nils-eilers/uMMF/doc/8032030-6.gif

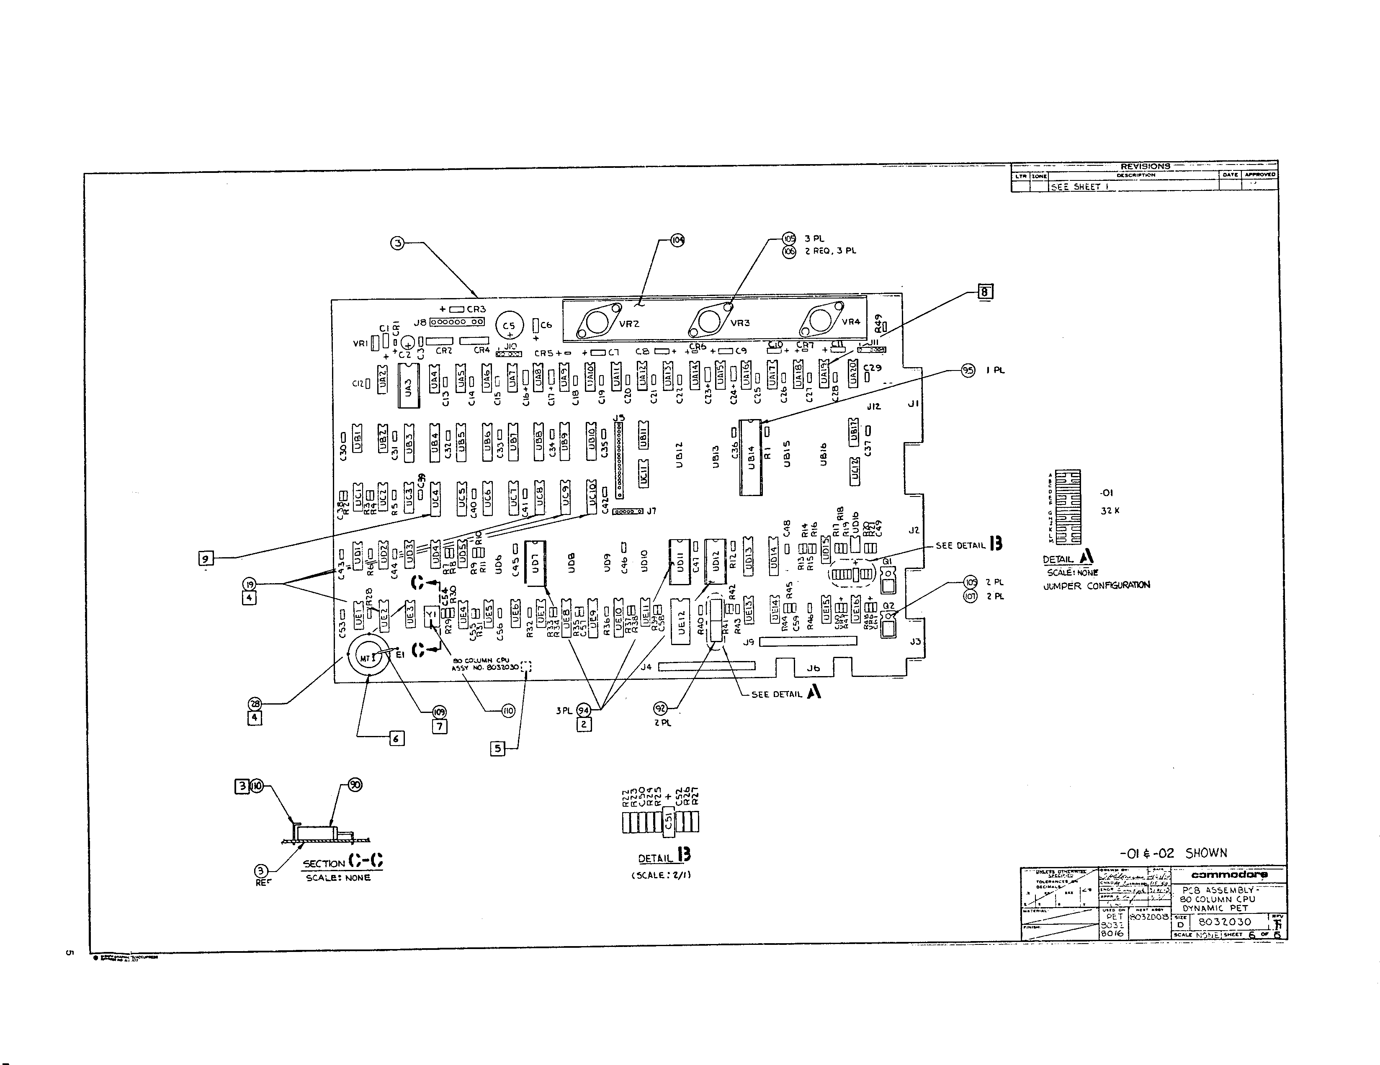
doc/8032030-6.gif
