nils-eilers/uMMF/doc/8032080-7.gif

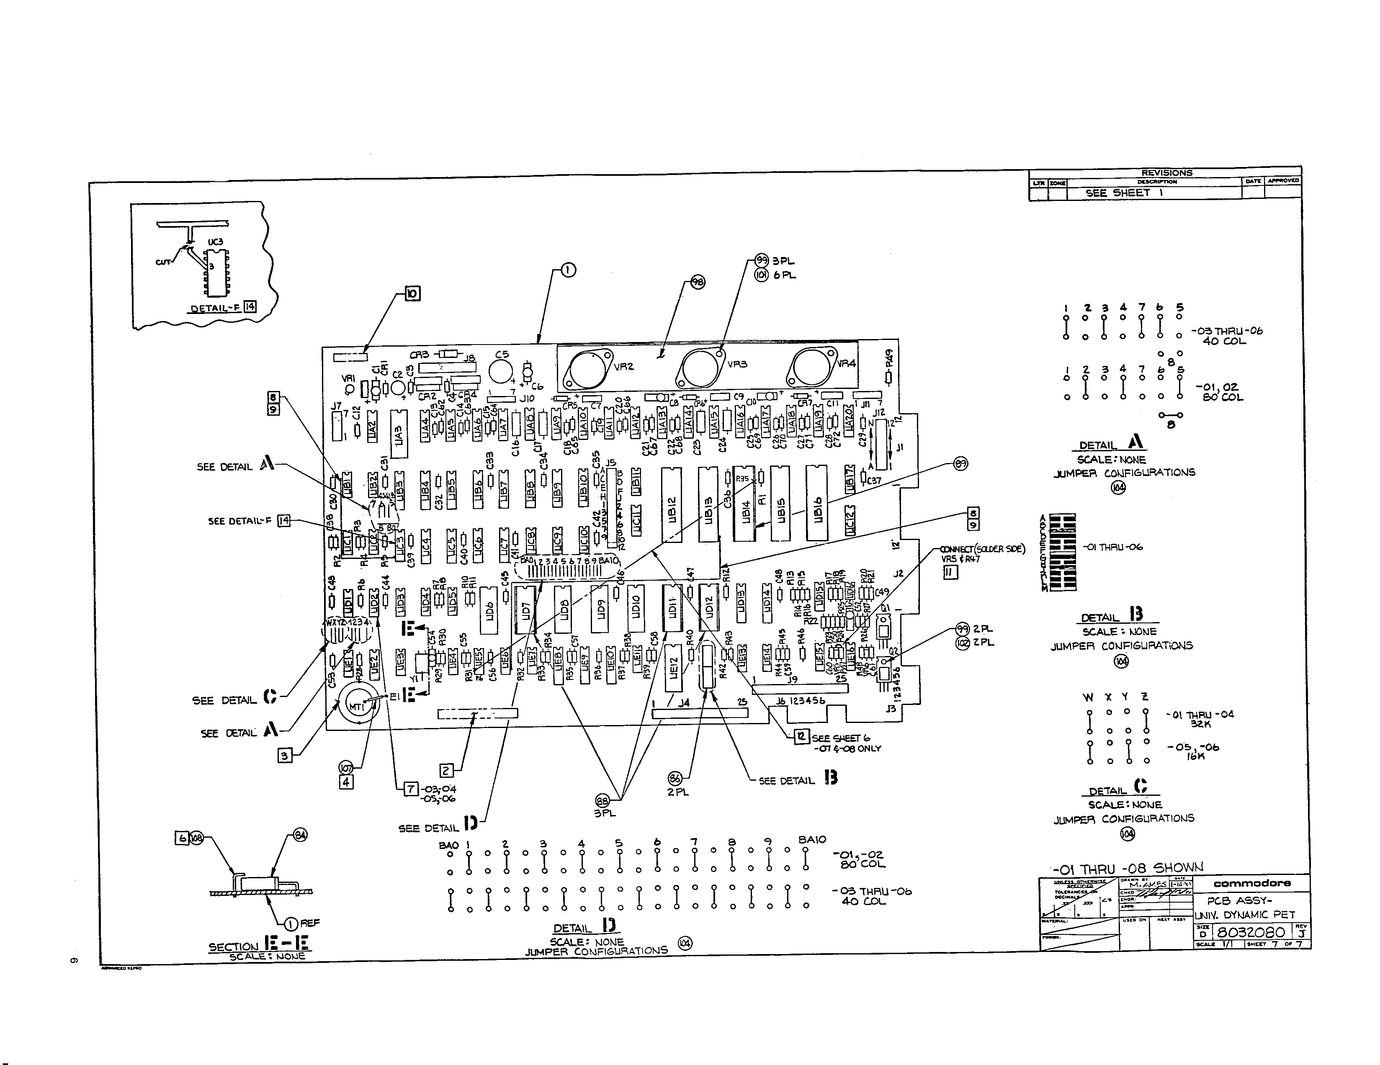
doc/8032080-7.gif
