nils-eilers/uMMF/doc/8032090-7.gif

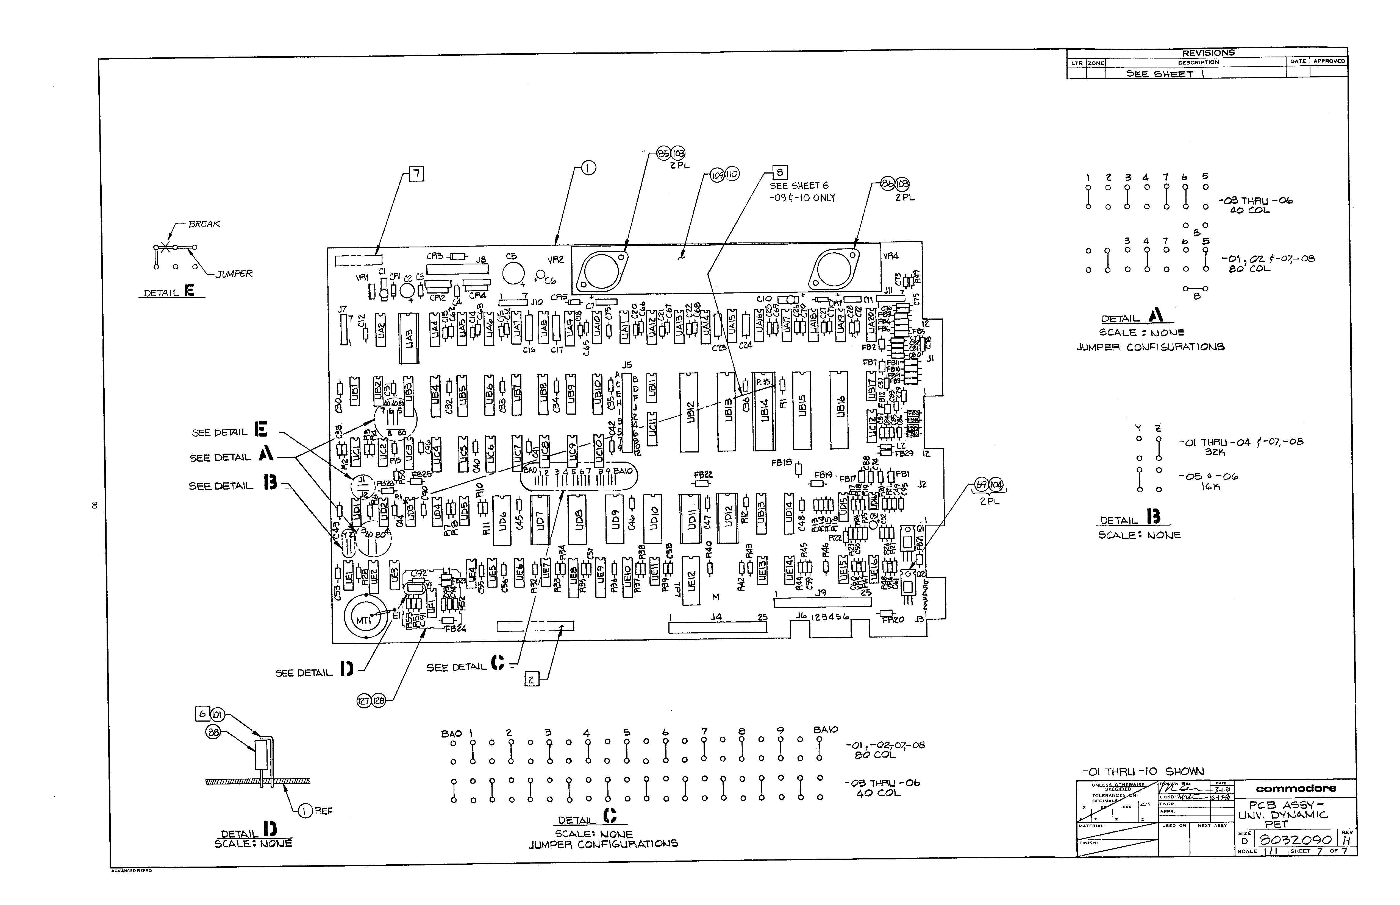
doc/8032090-7.gif
